TETRA888/Profilometer/Code/Software/3DProfile.png

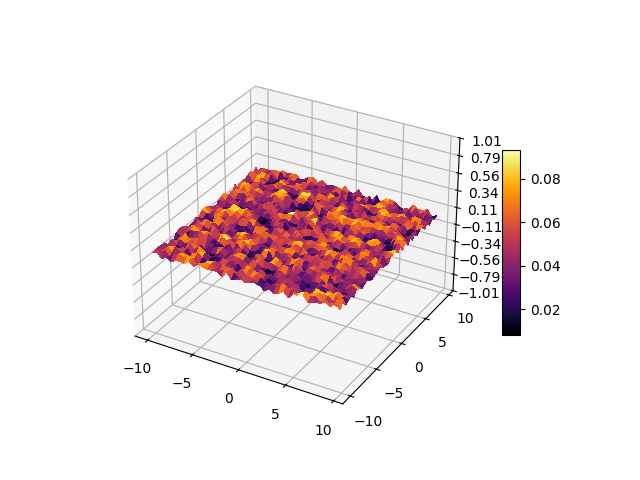
Code/Software/3DProfile.png
