TETRA888/Profilometer/Code/Software/profileGraph.png

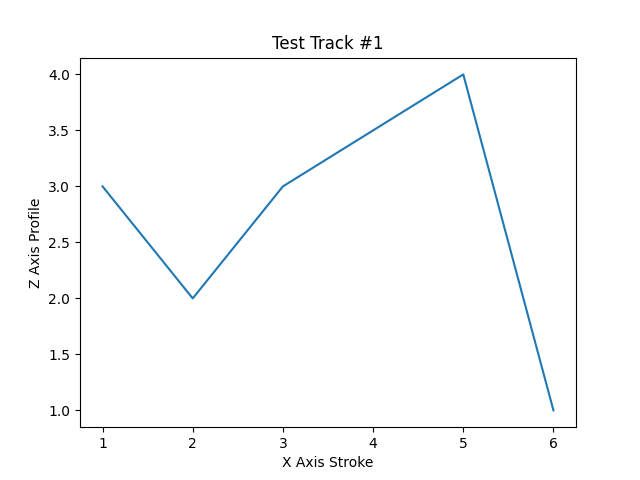
Code/Software/profileGraph.png
