TETRA888/Profilometer/FlowDiagrams/HighLevelSoftwareSystemDiagram.png

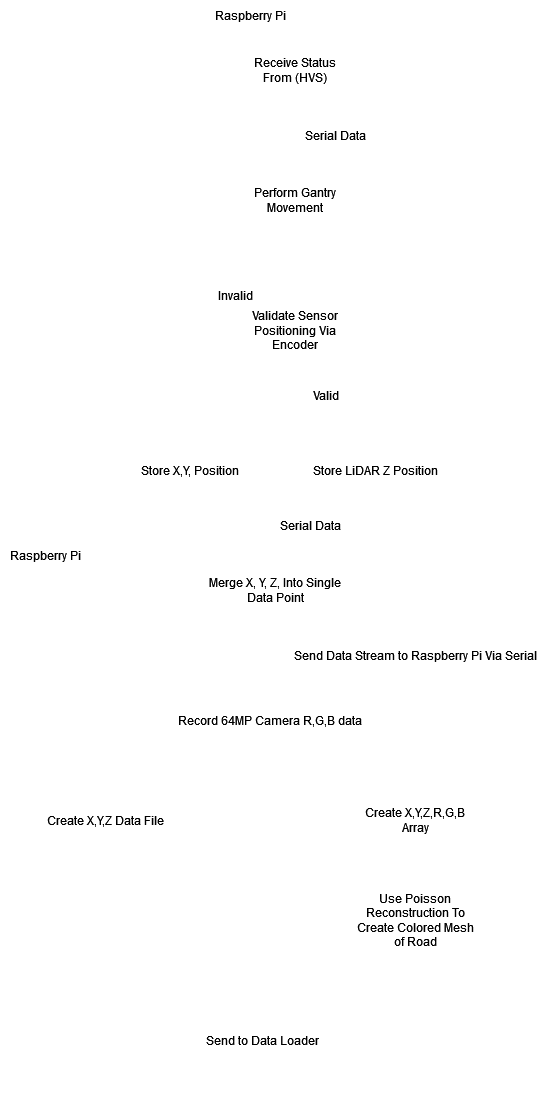
FlowDiagrams/HighLevelSoftwareSystemDiagram.png
