TETRA888/Profilometer/ProfilerBrackets/ProximityBrackets.png

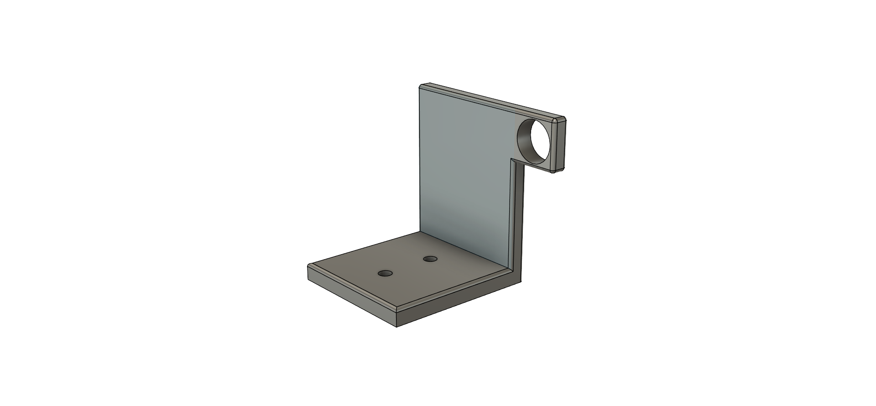
ProfilerBrackets/ProximityBrackets.png
