TETRA888/Profilometer/ProfilerBrackets/PulleyBrackets.png

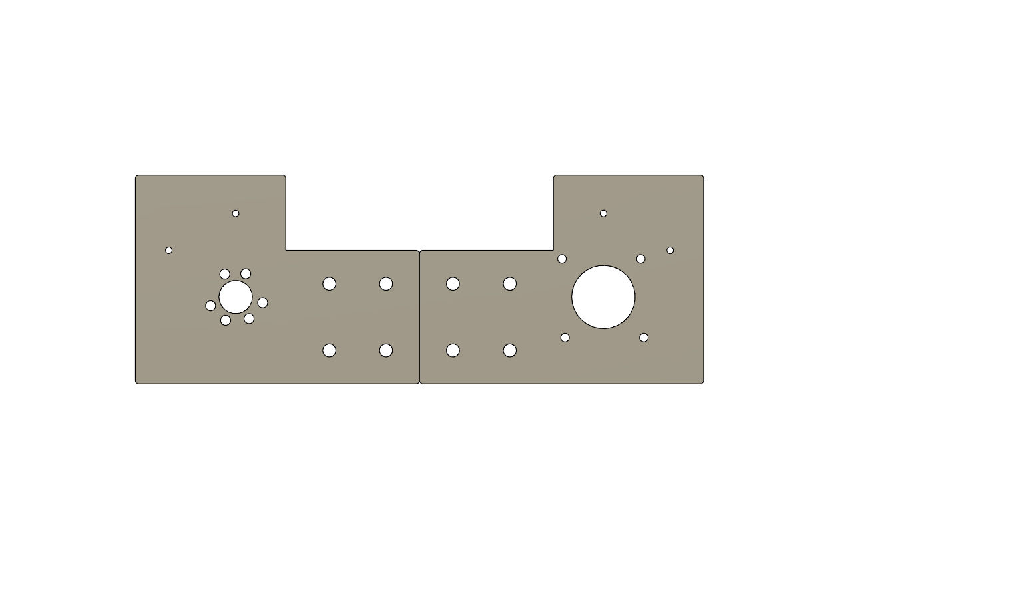
ProfilerBrackets/PulleyBrackets.png
